duokino/linerbot/images/127280194_10218643802187651_53932526784911531_n.jpg

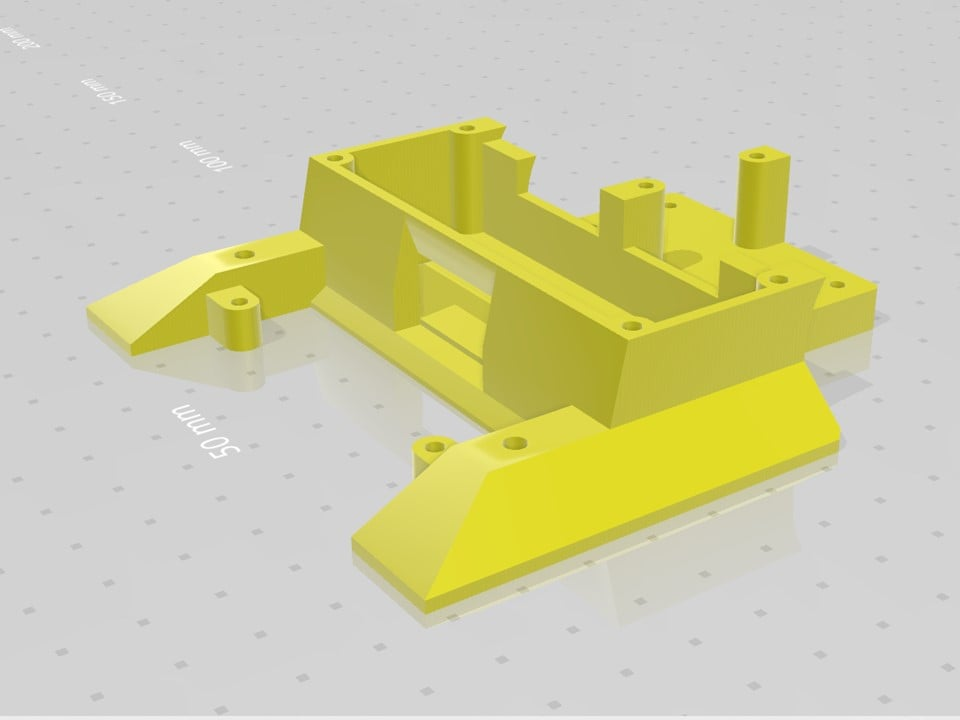
images/127280194_10218643802187651_53932526784911531_n.jpg
