duokino/linerbot/images/130723497_10218762713240353_1042097733240203540_o.jpg

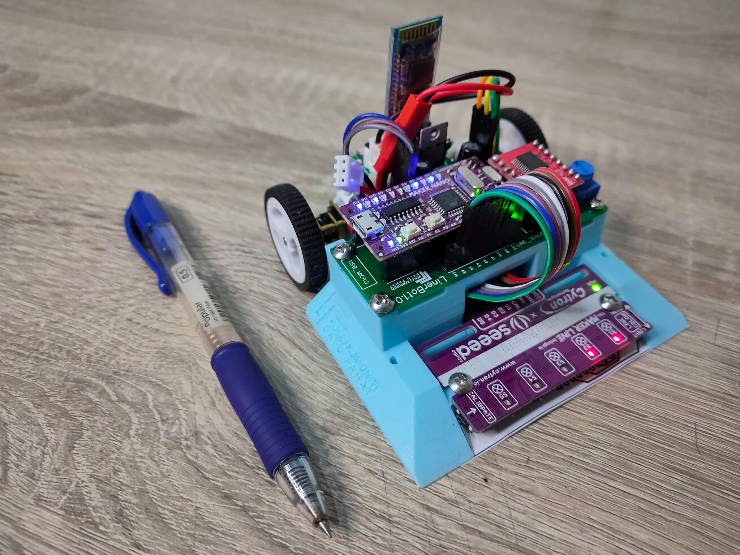
images/130723497_10218762713240353_1042097733240203540_o.jpg
