duokino/linerbot/images/131342407_10218762712320330_1406382797130012025_p.jpg

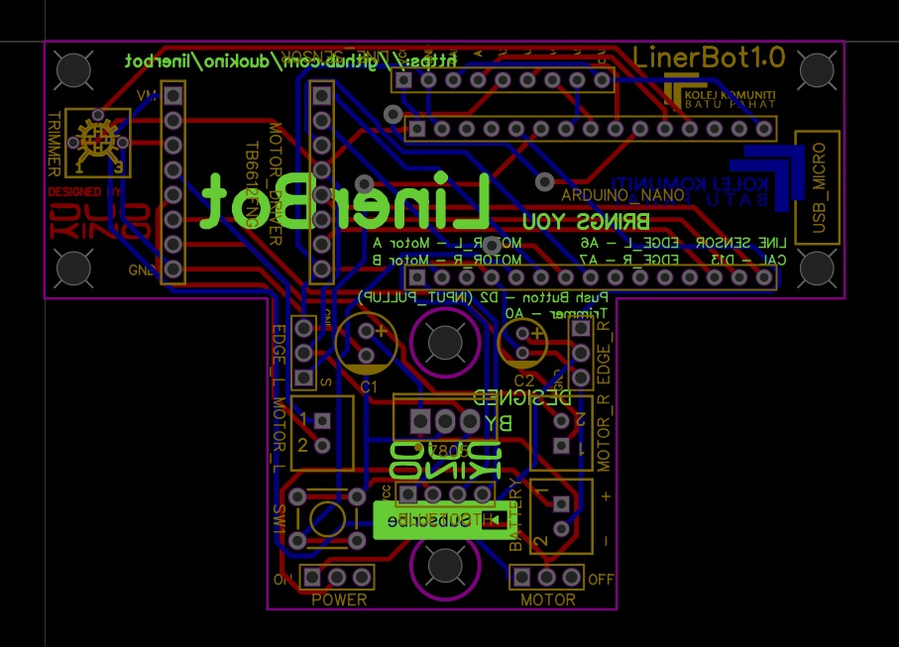
images/131342407_10218762712320330_1406382797130012025_p.jpg
